lultoni/pengo-keyboard/ergogen/output/outlines/key_cut_left.dxf

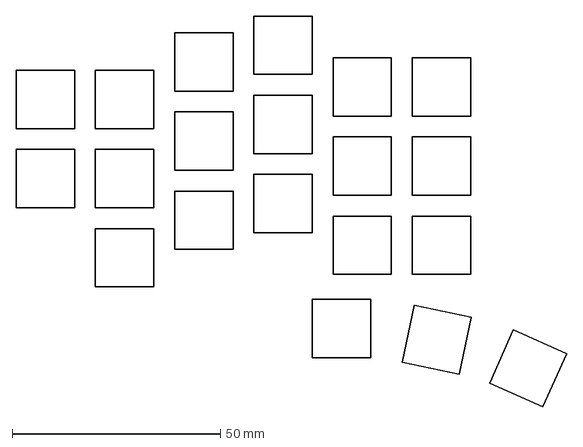
[picture p31: CAD file, 2024-10-01]
ergogen/output/outlines/key_cut_left.dxf
132.1 x 93.8 mm
