lultoni/pengo-keyboard/ergogen/output/outlines/xl_board_key_cutouts.dxf

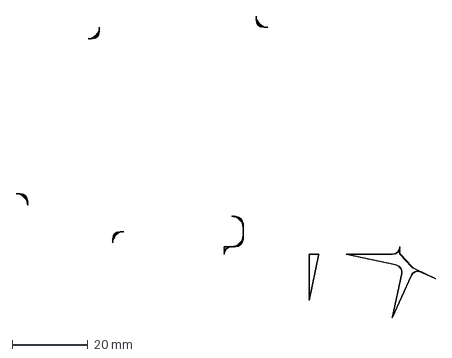
[picture p32: CAD file, 2024-09-30]
ergogen/output/outlines/xl_board_key_cutouts.dxf
111.0 x 79.8 mm
