lultoni/pengo-keyboard/ergogen/output/outlines/board_right.dxf

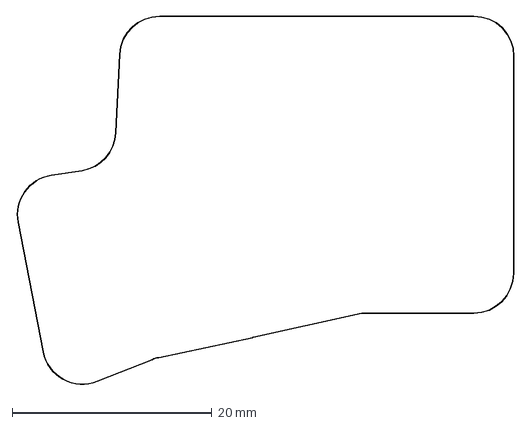
[picture p33: CAD file, 2024-09-25]
ergogen/output/outlines/board_right.dxf
49.8 x 37.0 mm
