lultoni/pengo-keyboard/ergogen/output/outlines/keys_left.dxf

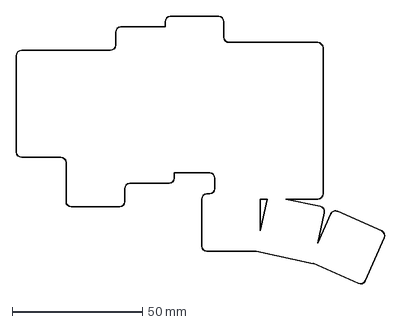
[picture p34: CAD file, 2024-09-25]
ergogen/output/outlines/keys_left.dxf
141.5 x 102.8 mm
