lultoni/pengo-keyboard/ergogen/output/outlines/keys_right.dxf

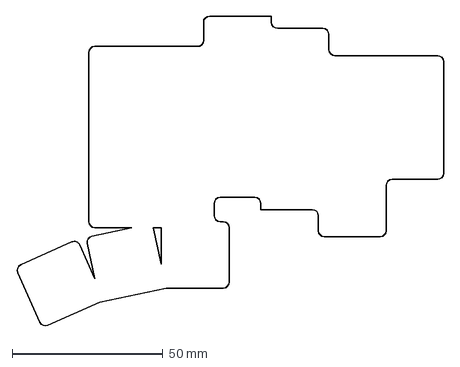
[picture p35: CAD file, 2024-09-25]
ergogen/output/outlines/keys_right.dxf
141.5 x 102.8 mm
