lultoni/pengo-keyboard/ergogen/output/outlines/board_left.dxf

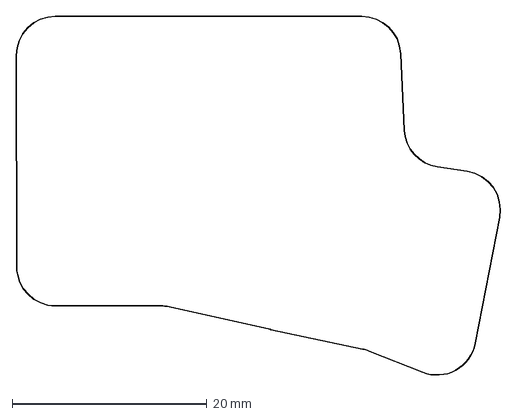
[picture p36: CAD file, 2024-09-25]
ergogen/output/outlines/board_left.dxf
49.8 x 37.0 mm
